NielsLeenheer/Pixel/source/PixelServer/ip.ino

boolean isIp(String str) {
  for (int i = 0; i < str.length(); i++) {
    int c = str.charAt(i);
    if (c != '.' && (c < '0' || c > '9')) {
      return false;
    }
  }
  return true;
}

String toStringIp(IPAddress ip) {
  String res = "";
  for (int i = 0; i < 3; i++) {
    res += String((ip >> (8 * i)) & 0xFF) + ".";
  }
  res += String(((ip >> 8 * 3)) & 0xFF);
  return res;
}
